OddbitCoder/Partner40/ai/hardware/chips/LS04.md

# 74LS04 — Hex Inverter

## Overview
The 74LS04 contains six independent single-input inverting gates (NOT gates). The output of each gate is the logical complement of its input: a HIGH input produces a LOW output and vice versa. Outputs are standard push-pull (totem-pole) TTL with no 3-state or open-collector features. The hex inverter is among the most widely used logic chips in any digital design and appears in virtually every Z80-based computer for bus polarity inversion, active-level conversion, clock buffering, and oscillator feedback.

## Pinout
| Pin | Name | Type | Description |
|-----|---|---|---|
| 1 | 1A | I | Gate 1 input |
| 2 | 1Y | O | Gate 1 inverting output |
| 3 | 2A | I | Gate 2 input |
| 4 | 2Y | O | Gate 2 inverting output |
| 5 | 3A | I | Gate 3 input |
| 6 | 3Y | O | Gate 3 inverting output |
| 7 | GND | P | Ground (0 V) |
| 8 | 4A | I | Gate 4 input |
| 9 | 4Y | O | Gate 4 inverting output |
| 10 | 5A | I | Gate 5 input |
| 11 | 5Y | O | Gate 5 inverting output |
| 12 | 6A | I | Gate 6 input |
| 13 | 6Y | O | Gate 6 inverting output |
| 14 | VCC | P | Supply voltage (+5 V) |

## Notes
- Typical propagation delay is 15 ns (LS subfamily).
- The 74LS14 is pin-compatible but adds Schmitt-trigger hysteresis to each input for improved noise immunity.
- The 74LS05 is pin-compatible but has open-collector outputs, requiring external pull-up resistors.
- Two inverters in series produce a non-inverting buffer with a small delay; this technique is used when a standard non-inverting buffer chip is unavailable.
- In Z80 systems, the LS04 commonly inverts active-LOW signals to active-HIGH and vice versa, and is used in the oscillator/clock circuit together with a crystal.
