OddbitCoder/Partner40/ai/hardware/chips/LS05.md

# 74LS05 — Hex Inverter with Open-Collector Outputs

## Overview
The 74LS05 contains six independent single-input inverter (NOT) gates, each with an open-collector output. Because the outputs are open-collector rather than totem-pole, an external pull-up resistor is required on each output line. This makes the device suitable for wired-AND configurations, level shifting to higher voltages, and driving LEDs or other loads directly.

## Pinout
| Pin | Name | Type | Description |
|-----|---|---|---|
| 1 | 1A | I | Gate 1 input |
| 2 | 1Y | OC | Gate 1 output (open-collector) |
| 3 | 2A | I | Gate 2 input |
| 4 | 2Y | OC | Gate 2 output (open-collector) |
| 5 | 3A | I | Gate 3 input |
| 6 | 3Y | OC | Gate 3 output (open-collector) |
| 7 | GND | P | Ground (0 V) |
| 8 | 4Y | OC | Gate 4 output (open-collector) |
| 9 | 4A | I | Gate 4 input |
| 10 | 5Y | OC | Gate 5 output (open-collector) |
| 11 | 5A | I | Gate 5 input |
| 12 | 6Y | OC | Gate 6 output (open-collector) |
| 13 | 6A | I | Gate 6 input |
| 14 | VCC | P | Supply voltage (+5 V) |

## Notes
- Each output requires an external pull-up resistor (typically 1 kΩ–10 kΩ to VCC) to assert a logic HIGH.
- Open-collector outputs may be wire-ANDed together on a shared bus; the bus is LOW if any driver pulls it low.
- Maximum collector voltage on outputs is 5.5 V; maximum sink current is 8 mA (LS subfamily).
- Functionally equivalent to the 74LS04 except for the open-collector output structure.
- The 74LS06 is a higher-voltage (30 V) open-collector variant intended for interfacing to higher-level logic or relay drivers.
