OddbitCoder/Partner40/ai/hardware/chips/LS132.md

# 74LS132 — Quadruple 2-Input Schmitt-Trigger NAND Gate

## Overview
The 74LS132 contains four independent 2-input NAND gates, each with Schmitt-trigger inputs. The Schmitt-trigger action provides hysteresis: the positive-going input threshold (VT+) is higher than the negative-going threshold (VT−). This makes the device highly immune to noise and slow input transitions, producing clean, jitter-free outputs even when driven by slowly changing or noisy signals. It is electrically and pin-compatible with the 74LS00 but with the added Schmitt-trigger input conditioning.

## Pinout
| Pin | Name | Type | Description |
|-----|---|---|---|
| 1 | 1A | I | Gate 1 Schmitt-trigger input A |
| 2 | 1B | I | Gate 1 Schmitt-trigger input B |
| 3 | 1Y | O | Gate 1 output |
| 4 | 2A | I | Gate 2 Schmitt-trigger input A |
| 5 | 2B | I | Gate 2 Schmitt-trigger input B |
| 6 | 2Y | O | Gate 2 output |
| 7 | GND | P | Ground (0 V) |
| 8 | 3Y | O | Gate 3 output |
| 9 | 3A | I | Gate 3 Schmitt-trigger input A |
| 10 | 3B | I | Gate 3 Schmitt-trigger input B |
| 11 | 4Y | O | Gate 4 output |
| 12 | 4A | I | Gate 4 Schmitt-trigger input A |
| 13 | 4B | I | Gate 4 Schmitt-trigger input B |
| 14 | VCC | P | Supply voltage (+5 V) |

## Notes
- Typical hysteresis: VT+ ≈ 1.6 V, VT− ≈ 0.8 V (LS subfamily at 5 V, 25 °C), giving ~0.8 V of noise margin.
- Drop-in replacement for the 74LS00 in noise-sensitive circuits; logic function is identical (2-input NAND) but with hysteresis on inputs.
- Commonly used to debounce mechanical switches, condition slow RC-ramp signals, and regenerate degraded TTL clock edges.
- The four gates are fully independent; no shared enables or common control lines.
- Totem-pole outputs (not open-collector); outputs can source and sink current without external pull-up resistors.
