OddbitCoder/Partner40/ai/hardware/chips/LS244.md

# 74LS244 — Octal Buffer/Line Driver with 3-State Outputs

## Overview
The 74LS244 contains eight independent non-inverting buffer/line drivers arranged as two groups of four, each group sharing a common active-low output-enable (~1G and ~2G). When an enable is asserted LOW, the four corresponding outputs follow their inputs; when deasserted HIGH, those outputs float to a high-impedance (3-state) condition. The chip is designed to drive highly capacitive or low-impedance bus lines and is widely used as a unidirectional data/address bus driver in Z80 and similar microcomputer systems.

## Pinout
| Pin | Name | Type | Description |
|-----|---|---|---|
| 1 | ~1G | I | Group 1 output enable, active LOW |
| 2 | 1A1 | I | Group 1, buffer 1 input |
| 3 | 2Y4 | O | Group 2, buffer 4 output |
| 4 | 1A2 | I | Group 1, buffer 2 input |
| 5 | 2Y3 | O | Group 2, buffer 3 output |
| 6 | 1A3 | I | Group 1, buffer 3 input |
| 7 | 2Y2 | O | Group 2, buffer 2 output |
| 8 | 1A4 | I | Group 1, buffer 4 input |
| 9 | 2Y1 | O | Group 2, buffer 1 output |
| 10 | GND | P | Ground (0 V) |
| 11 | 2A1 | I | Group 2, buffer 1 input |
| 12 | 1Y4 | O | Group 1, buffer 4 output |
| 13 | 2A2 | I | Group 2, buffer 2 input |
| 14 | 1Y3 | O | Group 1, buffer 3 output |
| 15 | 2A3 | I | Group 2, buffer 3 input |
| 16 | 1Y2 | O | Group 1, buffer 2 output |
| 17 | 2A4 | I | Group 2, buffer 4 input |
| 18 | 1Y1 | O | Group 1, buffer 1 output |
| 19 | ~2G | I | Group 2 output enable, active LOW |
| 20 | VCC | P | Supply voltage (+5 V) |

## Notes
- All outputs are 3-state (high-impedance when enable is deasserted), making this device suitable for bidirectional bus architectures where multiple drivers share a bus.
- The two enable pins (~1G and ~2G) allow the chip to act as two independent 4-bit buffers or as a single 8-bit buffer when both enables are tied together.
- Commonly used to buffer the Z80 address bus, data bus, or control lines toward peripheral devices.
- A logic HIGH on an enable pin disables (floats) that group of outputs; a logic LOW enables them.
- Propagation delay is typically 12 ns; output enable/disable time is typically 18 ns.
