OddbitCoder/Partner40/ai/hardware/chips/LS38.md

# 74LS38 — Quadruple 2-Input NAND Buffer with Open-Collector Outputs

## Overview
The 74LS38 contains four independent 2-input NAND buffer gates, each with an open-collector output. The buffer designation indicates higher output drive capability compared to a standard gate. Because all outputs are open-collector, external pull-up resistors are required. Multiple outputs may be wire-ANDed together on a shared bus.

## Pinout
| Pin | Name | Type | Description |
|-----|---|---|---|
| 1 | 1A | I | Gate 1 input A |
| 2 | 1B | I | Gate 1 input B |
| 3 | 1Y | OC | Gate 1 output (open-collector) |
| 4 | 2A | I | Gate 2 input A |
| 5 | 2B | I | Gate 2 input B |
| 6 | 2Y | OC | Gate 2 output (open-collector) |
| 7 | GND | P | Ground (0 V) |
| 8 | 3Y | OC | Gate 3 output (open-collector) |
| 9 | 3A | I | Gate 3 input A |
| 10 | 3B | I | Gate 3 input B |
| 11 | 4Y | OC | Gate 4 output (open-collector) |
| 12 | 4A | I | Gate 4 input A |
| 13 | 4B | I | Gate 4 input B |
| 14 | VCC | P | Supply voltage (+5 V) |

## Notes
- Each output requires an external pull-up resistor (typically 1 kΩ–4.7 kΩ to VCC) to provide a logic HIGH level.
- Open-collector outputs can be wire-ANDed: the shared bus is LOW if any output pulls it low.
- The 74LS38 differs from the 74LS00 (totem-pole outputs) and 74LS01 (open-collector, standard drive) by providing buffered (higher drive) open-collector outputs.
- Useful for bus driving, level shifting, and interfacing TTL logic to higher-voltage systems.
