OddbitCoder/Partner40/ai/hardware/chips/LS42.md

# 74LS42 — BCD-to-Decimal Decoder

## Overview
The 74LS42 decodes a 4-bit BCD (Binary-Coded Decimal) input (A0–A3) into one of ten active-LOW outputs (Q0–Q9), each corresponding to a decimal digit 0 through 9. Only one output is asserted LOW at a time, based on the binary value of the input. For invalid BCD codes (10–15), all ten outputs remain HIGH. The device is housed in a 16-pin DIP.

## Pinout
| Pin | Name | Type | Description |
|-----|---|---|---|
| 1 | Q0 | O | Decimal output 0 (active LOW) |
| 2 | Q1 | O | Decimal output 1 (active LOW) |
| 3 | Q2 | O | Decimal output 2 (active LOW) |
| 4 | Q3 | O | Decimal output 3 (active LOW) |
| 5 | Q4 | O | Decimal output 4 (active LOW) |
| 6 | Q5 | O | Decimal output 5 (active LOW) |
| 7 | Q6 | O | Decimal output 6 (active LOW) |
| 8 | GND | P | Ground (0 V) |
| 9 | Q7 | O | Decimal output 7 (active LOW) |
| 10 | Q8 | O | Decimal output 8 (active LOW) |
| 11 | Q9 | O | Decimal output 9 (active LOW) |
| 12 | A3 | I | BCD input bit 3 (weight 8) |
| 13 | A2 | I | BCD input bit 2 (weight 4) |
| 14 | A1 | I | BCD input bit 1 (weight 2) |
| 15 | A0 | I | BCD input bit 0 (weight 1) |
| 16 | VCC | P | Supply voltage (+5 V) |

## Notes
- Outputs are active LOW: the selected output is pulled to logic 0; all unselected outputs remain HIGH.
- Input codes 1010–1111 (10–15) are invalid BCD; all outputs remain HIGH for these combinations.
- Commonly used to decode address lines or to select one of up to ten peripheral devices or memory banks.
- Directly interfaces with TTL, CMOS, NMOS, and LED/display drivers.
- The 74LS138 (3-to-8 decoder) or 74LS154 (4-to-16 decoder) are alternatives when more outputs are needed.
