OddbitCoder/Partner40/ai/hardware/chips/LS86.md

# 74LS86 — Quadruple 2-Input XOR Gate

## Overview
The 74LS86 contains four independent 2-input Exclusive-OR (XOR) gates. The output of each gate is HIGH when its two inputs differ (one HIGH, one LOW) and LOW when both inputs are the same (both HIGH or both LOW). XOR gates are fundamental building blocks for binary adders, parity generators/checkers, comparators, and controlled inverters (using one input as a data line and the other as an invert-enable).

## Pinout
| Pin | Name | Type | Description |
|-----|---|---|---|
| 1 | 1A | I | Gate 1 input A |
| 2 | 1B | I | Gate 1 input B |
| 3 | 1Y | O | Gate 1 output (A XOR B) |
| 4 | 2A | I | Gate 2 input A |
| 5 | 2B | I | Gate 2 input B |
| 6 | 2Y | O | Gate 2 output (A XOR B) |
| 7 | GND | P | Ground (0 V) |
| 8 | 3Y | O | Gate 3 output (A XOR B) |
| 9 | 3A | I | Gate 3 input A |
| 10 | 3B | I | Gate 3 input B |
| 11 | 4Y | O | Gate 4 output (A XOR B) |
| 12 | 4A | I | Gate 4 input A |
| 13 | 4B | I | Gate 4 input B |
| 14 | VCC | P | Supply voltage (+5 V) |

## Notes
- Truth table per gate: Y = A ⊕ B; output is HIGH only when inputs are different.
- Controlled inverter: tying one input HIGH forces the output to be the complement of the other input; tying one input LOW passes the other input unchanged.
- Four gates per package allow construction of a 4-bit parity tree or a 4-bit comparator stage.
- Typical propagation delay: ~22 ns HIGH-to-LOW, ~17 ns LOW-to-HIGH (LS subfamily at 5 V, 25 °C).
