OddbitCoder/Partner40/ai/hardware/chips/M2716.md

# M2716 — Intel/SGS-Thomson 2716 16K (2K×8) UV-Erasable EPROM

## Overview
The 2716 (Intel original; SGS-Thomson M2716; equivalent second-sources from AMD, NEC, Fujitsu, etc.) is a 16,384-bit UV-erasable and electrically programmable read-only memory organised as 2,048 words of 8 bits. It operates from a single +5 V supply during normal reads, making it directly compatible with Z80 and 8080-family systems. Programming requires a 25 V programming supply on VPP. The chip is erased by exposure to shortwave (2537 Å) ultraviolet light through the quartz window; a total UV dosage of 15 Ws/cm² is required for a full erase (typically 20–30 minutes with a standard UV lamp at 2.5 cm). The 24-pin DIP package with a transparent window lid is the standard form factor. Access time is 450 ns (standard) or 350 ns (M2716-1).

## Pinout

| Pin | Name | Type | Description |
|--|--|--|--|
| 1 | A7 | I | Address Input Bit 7. |
| 2 | A6 | I | Address Input Bit 6. |
| 3 | A5 | I | Address Input Bit 5. |
| 4 | A4 | I | Address Input Bit 4. |
| 5 | A3 | I | Address Input Bit 3. |
| 6 | A2 | I | Address Input Bit 2. |
| 7 | A1 | I | Address Input Bit 1. |
| 8 | A0 | I | Address Input Bit 0. |
| 9 | Q0 | O | Data Output Bit 0 (three-state). |
| 10 | Q1 | O | Data Output Bit 1 (three-state). |
| 11 | Q2 | O | Data Output Bit 2 (three-state). |
| 12 | VSS | P | Ground (0 V). |
| 13 | Q3 | O | Data Output Bit 3 (three-state). |
| 14 | Q4 | O | Data Output Bit 4 (three-state). |
| 15 | Q5 | O | Data Output Bit 5 (three-state). |
| 16 | Q6 | O | Data Output Bit 6 (three-state). |
| 17 | Q7 | O | Data Output Bit 7 (three-state). |
| 18 | EP | I | Chip Enable / Program (active low). Low selects the chip for read; a 45–55 ms TTL pulse here (with VPP = 25 V) programs one byte. High puts the chip into low-power standby mode (outputs Hi-Z). |
| 19 | A10 | I | Address Input Bit 10 (MSB of the 11-bit address). |
| 20 | G | I | Output Enable (active low). Low enables the three-state outputs; high forces outputs to Hi-Z regardless of EP. |
| 21 | VPP | P | Programming Supply. +5 V during read; +25 V (±1 V) during programming. Must not exceed 26.5 V. |
| 22 | A9 | I | Address Input Bit 9. |
| 23 | A8 | I | Address Input Bit 8. |
| 24 | VCC | P | Positive Supply (+5 V ±5%). |

## Notes
- There are 11 address lines (A0–A10) selecting 2,048 byte locations.
- Three operating modes: (1) Read — EP low, G low, VPP = 5 V; (2) Standby — EP high, outputs Hi-Z, power reduced to ~25 mA; (3) Deselect — G high, outputs Hi-Z independent of EP.
- For programming, VCC and VPP must both be at +5 V and +25 V respectively before EP goes low; the program pulse is 45–55 ms on EP. Multiple 2716s can be programmed simultaneously with different data by controlling individual EP lines while sharing address and data buses.
- The outputs are TRI-STATE and can be wire-OR'd for memory expansion; any number of devices can share the same data bus provided only one EP and G are asserted at a time.
- Direct Intel 2716 equivalents include AMD AM2716, NEC D2716, Fujitsu MBM2716, Motorola MCM2716, and the SGS-Thomson M2716; all are pin-for-pin compatible.
