OddbitCoder/Partner40/ai/hardware/chips/S04.md

# 74S04 — Hex Inverter (Schottky)

## Overview
The 74S04 contains six independent single-input inverting gates (NOT gates) implemented in the Schottky TTL (74S) process. Schottky clamping diodes prevent transistors from saturating deeply, resulting in significantly faster switching than standard 74LS devices at the cost of higher quiescent power dissipation. The logic function is identical to the 74LS04 and the pinout is fully compatible; the 74S04 is a drop-in speed upgrade used where propagation delay is critical — for example in high-frequency clock buffering or fast-edge signal conditioning in Z80 systems running at the top of their specified clock range.

## Pinout
| Pin | Name | Type | Description |
|-----|---|---|---|
| 1 | 1A | I | Gate 1 input |
| 2 | 1Y | O | Gate 1 inverting output |
| 3 | 2A | I | Gate 2 input |
| 4 | 2Y | O | Gate 2 inverting output |
| 5 | 3A | I | Gate 3 input |
| 6 | 3Y | O | Gate 3 inverting output |
| 7 | GND | P | Ground (0 V) |
| 8 | 4A | I | Gate 4 input |
| 9 | 4Y | O | Gate 4 inverting output |
| 10 | 5A | I | Gate 5 input |
| 11 | 5Y | O | Gate 5 inverting output |
| 12 | 6A | I | Gate 6 input |
| 13 | 6Y | O | Gate 6 inverting output |
| 14 | VCC | P | Supply voltage (+5 V) |

## Notes
- Typical propagation delay is 3 ns, compared to ~15 ns for 74LS04 and ~9 ns for 74F04.
- Quiescent power dissipation is approximately 600 mW per package (full load), considerably higher than the 74LS04 (~90 mW).
- Fully pin-compatible with 74LS04, 74S04, 74F04, and 74HC04; can replace any of these in a circuit if the supply current budget allows.
- The 74S04 is typically found in the clock path of older Z80 designs where the crystal oscillator, clock buffer, and phase-inversion chain require minimal delay to stay within setup/hold margins.
- Input voltage levels and output drive specifications are standard TTL; fan-out is 10 LS loads per output.
