OddbitCoder/Partner40/ai/hardware/chips/Z80A SIO-1.md

# Z80A SIO/1 — Z8441 Serial Input/Output Controller

## Overview
The Z80A SIO/1 (Zilog Z8441) is a dual-channel serial communications controller in a 40-pin DIP package. It provides two independent full-duplex serial channels (A and B) supporting synchronous and asynchronous data formats including SDLC/HDLC, IBM Bisync, and monosync. Each channel has a dedicated baud-rate clock input for both transmit and receive, and supports programmable character lengths, parity, and stop bits in async mode. The SIO/1 variant is distinguished from SIO/0 (Z8440) and SIO/2 (Z8442) by its modem-control pin assignments: it provides W/RDYA and W/RDYB (Wait/Ready) outputs on both channels but omits DTRB, whereas SIO/0 provides full DTR and DCD modem signals on both channels and SIO/2 omits modem signals entirely. The W/RDY pins can be programmed as either CPU wait signals or DMA ready signals. All active-low signals are denoted with a leading slash.

## Pinout

| Pin | Name | Type | Description |
|-----|---|---|---|
| 1 | A/B | I | Channel select — high selects channel B, low selects channel A |
| 2 | C/D | I | Control/Data select — high selects control register, low selects data register |
| 3 | /CE | I | Chip enable — enables data transfer between CPU and SIO when low; active low |
| 4 | D0 | I/O | System data bus bit 0, LSB (3-state, bidirectional) |
| 5 | D1 | I/O | System data bus bit 1 (3-state, bidirectional) |
| 6 | D2 | I/O | System data bus bit 2 (3-state, bidirectional) |
| 7 | D3 | I/O | System data bus bit 3 (3-state, bidirectional) |
| 8 | D4 | I/O | System data bus bit 4 (3-state, bidirectional) |
| 9 | D5 | I/O | System data bus bit 5 (3-state, bidirectional) |
| 10 | D6 | I/O | System data bus bit 6 (3-state, bidirectional) |
| 11 | D7 | I/O | System data bus bit 7, MSB (3-state, bidirectional) |
| 12 | GND | P | Ground |
| 13 | /RESET | I | Reset — clears all internal registers and halts both channels; active low |
| 14 | /M1 | I | Machine cycle 1 from Z80 CPU — used with /IORQ for interrupt acknowledge |
| 15 | /IORQ | I | I/O request from Z80 CPU, active low |
| 16 | /RD | I | Read cycle status from Z80 CPU, active low |
| 17 | CLK | I | System clock, single-phase |
| 18 | /INT | OC | Interrupt request to Z80 CPU, open-drain, active low |
| 19 | IEI | I | Interrupt enable in — active high; Z80 daisy-chain priority interrupt input |
| 20 | IEO | O | Interrupt enable out — active high; propagates enable to next device in daisy chain |
| 21 | RxDA | I | Receive data channel A — serial data input, active high (mark = high) |
| 22 | RxCA | I | Receive clock channel A — clocks data into receive shift register |
| 23 | TxDA | O | Transmit data channel A — serial data output, active high |
| 24 | TxCA | I | Transmit clock channel A — clocks data out of transmit shift register |
| 25 | SYNCA | I/O | Sync character detect / external sync input for channel A; in auto-enable mode acts as sync output |
| 26 | W/RDYA | O | Wait/Ready channel A — programmable: acts as /WAIT to CPU (open-drain) or as RDY to DMA controller |
| 27 | /RTSA | O | Request to send channel A — modem control output, active low |
| 28 | /CTSA | I | Clear to send channel A — modem control input, active low; can gate transmitter |
| 29 | /DTRA | O | Data terminal ready channel A — modem control output, active low |
| 30 | /DCDA | I | Data carrier detect channel A — modem status input, active low |
| 31 | RxDB | I | Receive data channel B — serial data input, active high |
| 32 | RxCB | I | Receive clock channel B |
| 33 | TxDB | O | Transmit data channel B — serial data output, active high |
| 34 | TxCB | I | Transmit clock channel B |
| 35 | SYNCB | I/O | Sync character detect / external sync for channel B |
| 36 | W/RDYB | O | Wait/Ready channel B — programmable: acts as /WAIT to CPU (open-drain) or RDY to DMA |
| 37 | /RTSB | O | Request to send channel B, active low |
| 38 | /CTSB | I | Clear to send channel B, active low |
| 39 | /DCDB | I | Data carrier detect channel B — modem status input, active low |
| 40 | VCC | P | +5 V power supply |

## Notes
- The SIO/1 (Z8441) differs from SIO/0 (Z8440) in that channel B omits DTRB (present on SIO/0 pin 39) and instead provides W/RDYB on both channels; channel A retains /DTRA and /DCDA as on SIO/0.
- The SIO/2 (Z8442) omits all modem control signals on both channels; the SIO/1 is a compromise retaining full modem control on channel A.
- A/B and C/D are typically connected to address lines A1 and A0 respectively, giving four addressable registers (channel A data, channel A control, channel B data, channel B control).
- Both TxC and RxC on each channel can accept an external baud-rate clock, typically generated by a Z80 CTC channel whose ZC/TO output feeds the SIO clock input.
- The W/RDY pins are open-drain when configured as WAIT outputs, allowing them to be wire-ORed with other WAIT sources on the system bus.
- SDLC/HDLC mode provides automatic zero-insertion (bit stuffing), FCS generation and checking, and abort sequence detection.
- Each channel's interrupt vector is based on the vector register and the source (Rx, Tx, or special condition), with channel A having higher interrupt priority than channel B within the chip.
